Imperious22M/UltraGPS-Models/Transmitter-Models/Solidwork/Transmitter-tower-middle-2.SLDPRT

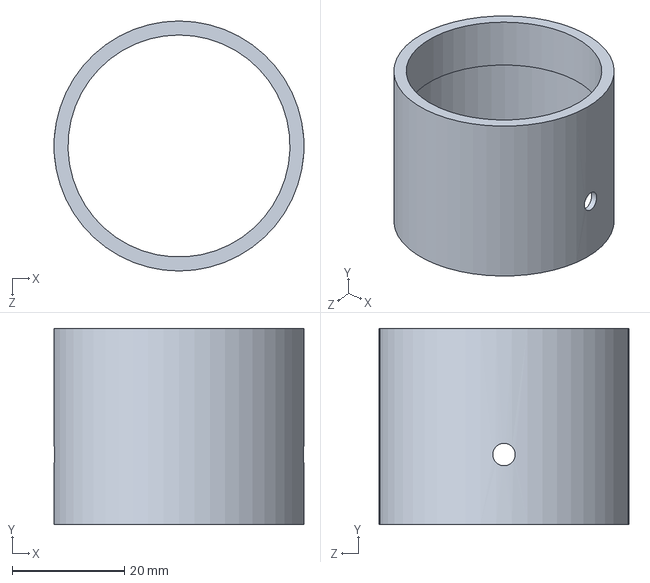
[picture p11: CAD file, 2026-09-30]
Transmitter-Models/Solidwork/Transmitter-tower-middle-2.SLDPRT
44.6 x 35.0 x 44.6 mm
