Imperious22M/UltraGPS-Models/Receiver-Arena-Models/Solidwork/Receiver-Parts/Transmitter-holder-single-top.SLDPRT

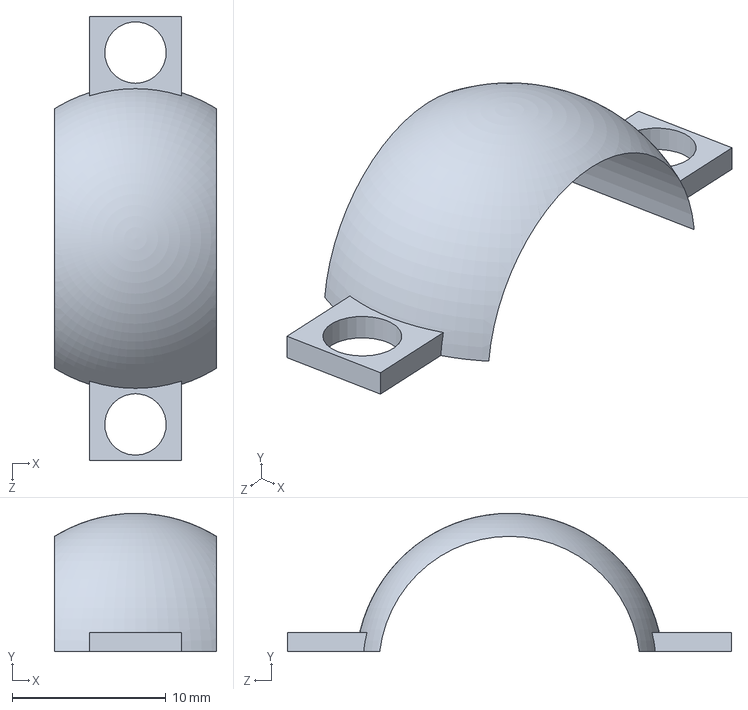
[picture p12: CAD file, 2026-09-30]
Receiver-Arena-Models/Solidwork/Receiver-Parts/Transmitter-holder-single-top.SLDPRT
10.5 x 9.00 x 28.9 mm
