Imperious22M/UltraGPS-Models/Receiver-Arena-Models/Solidwork/Receiver-Parts/ReceiverWboard.SLDPRT

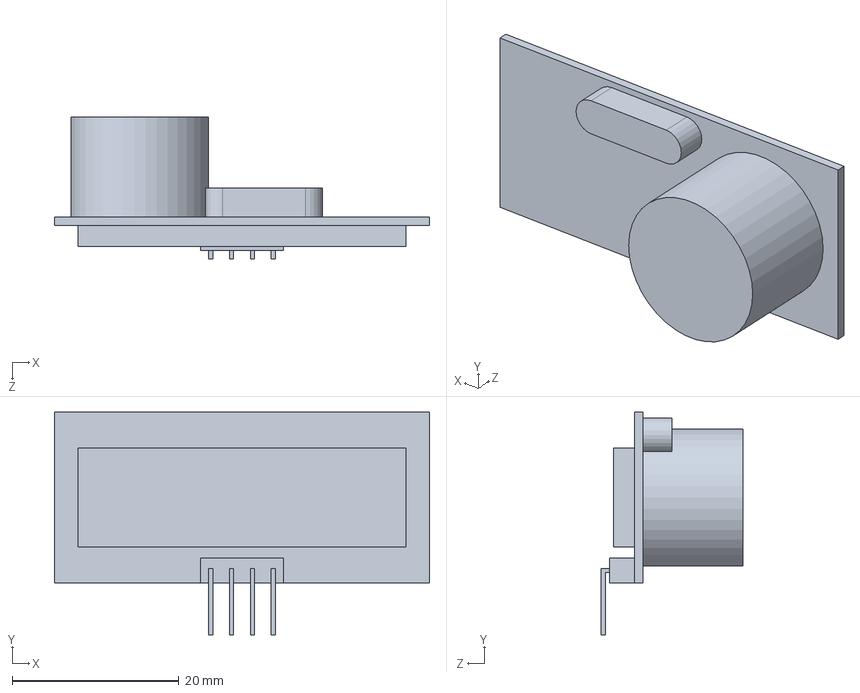
[picture p13: CAD file, 2026-09-30]
Receiver-Arena-Models/Solidwork/Receiver-Parts/ReceiverWboard.SLDPRT
45.0 x 26.8 x 17.0 mm
