Imperious22M/UltraGPS-Models/Transmitter-Models/STL/Transmitter-tower-middle.STL

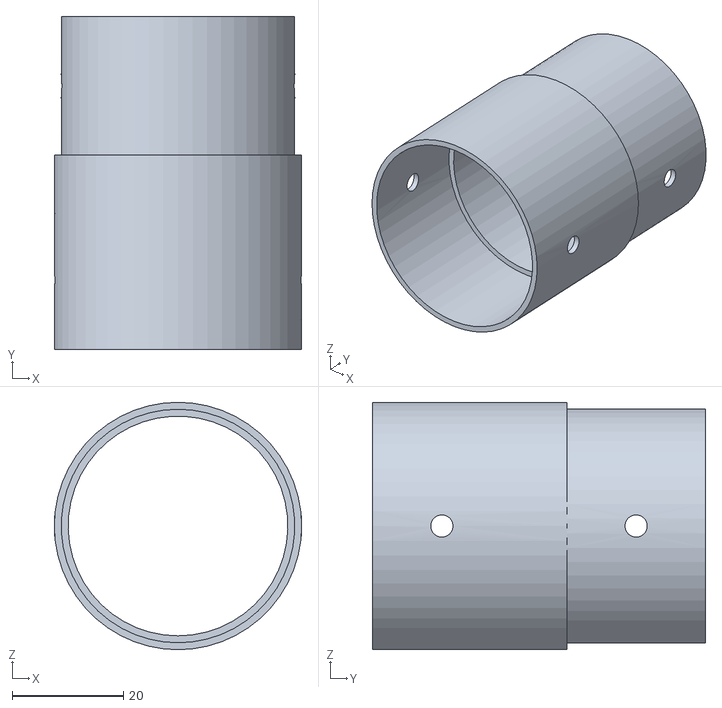
[picture p14: CAD file, 2026-09-30]
Transmitter-Models/STL/Transmitter-tower-middle.STL
44.6 x 60.0 x 44.6
